lshachar/Arduino_Fanatec_Wheel/Steering Wheel Photos/2020-03-29 04.41.28.jpg

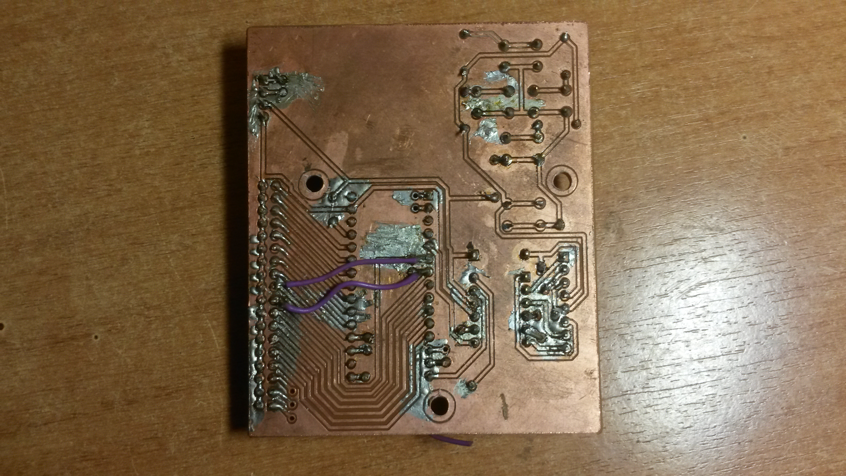
Steering Wheel Photos/2020-03-29 04.41.28.jpg
