lshachar/Arduino_Fanatec_Wheel/Steering Wheel Photos/2020-04-09 08.03.49.jpg

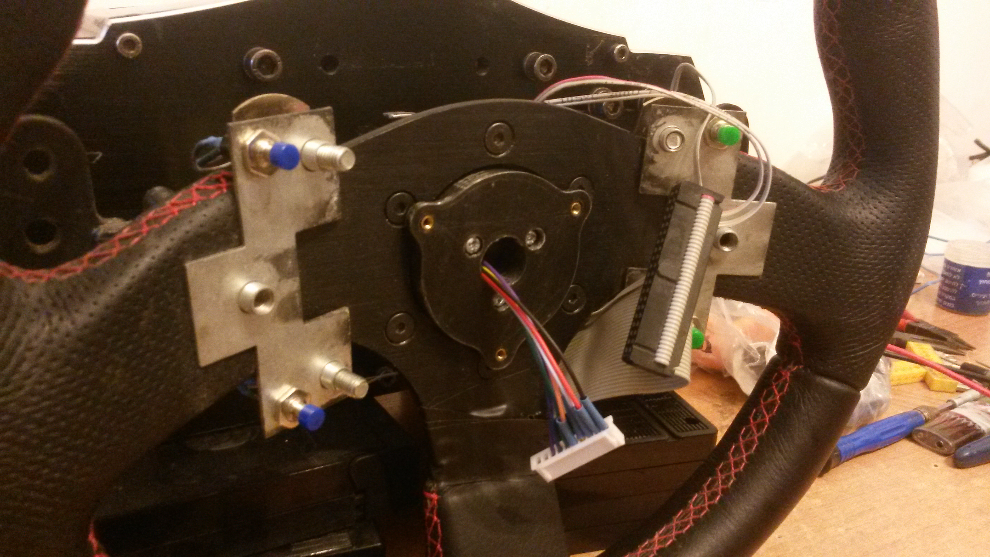
Steering Wheel Photos/2020-04-09 08.03.49.jpg
