lshachar/Arduino_Fanatec_Wheel/Steering Wheel Photos/2020-04-09 08.04.06.jpg

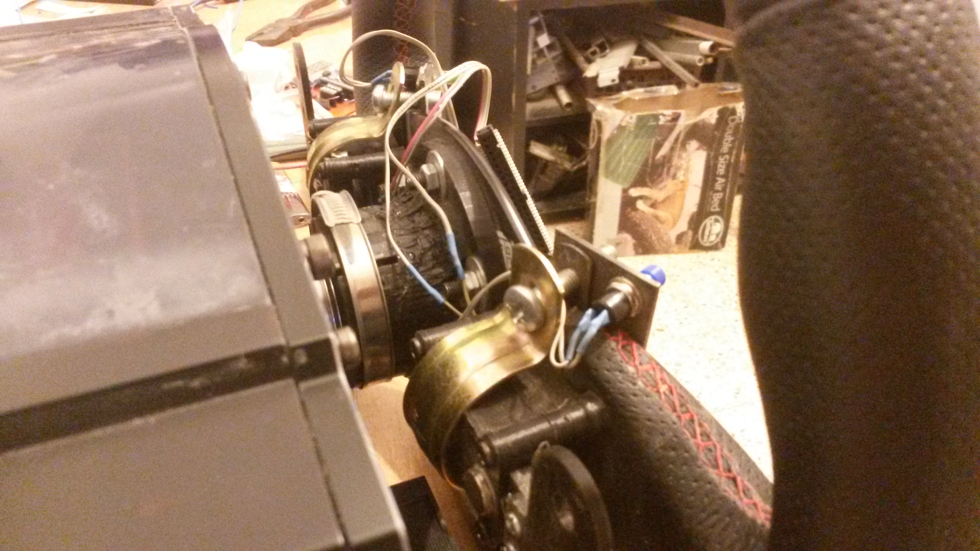
Steering Wheel Photos/2020-04-09 08.04.06.jpg
