lshachar/Arduino_Fanatec_Wheel/3d Models/mangentic pedal shifters/Imported to Solidworks/shifter_unit_switch_stop_plate.SLDPRT

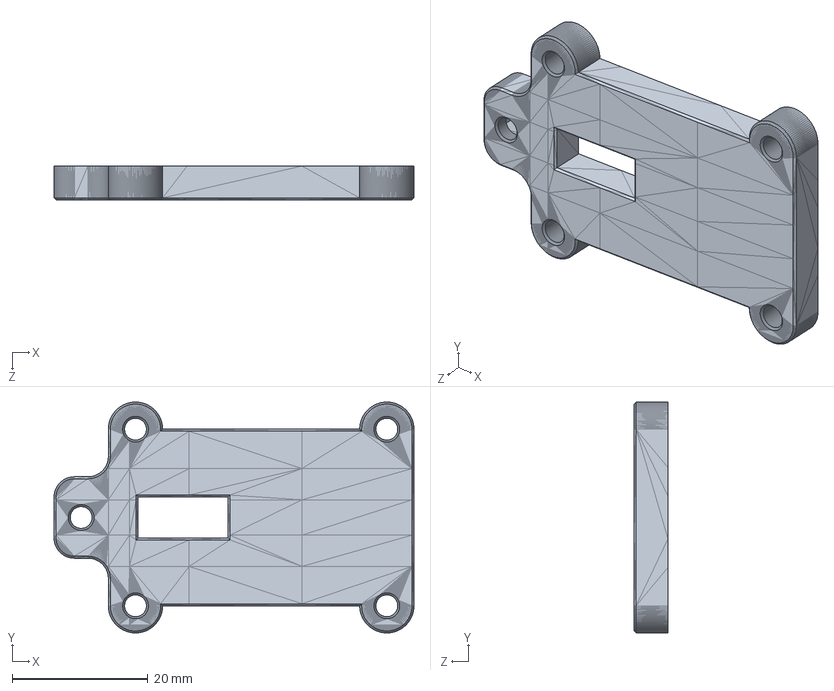
[picture p30: CAD file, 2020-04-10]
3d Models/mangentic pedal shifters/Imported to Solidworks/shifter_unit_switch_stop_plate.SLDPRT
53.0 x 34.0 x 5.00 mm
